mattysc42/IoT_midterm_remote/midterm_remote/src/playlist.h

#ifndef _PLAYLIST_H_
#define _PLAYLIST_H_

switch (currentTrack) {
    case 1: 
        myOLED.printf("Disturbed: \nRemnants");
        break;
    case 2: 
        myOLED.printf("Fastball: \nThe Way");
        break;
    case 3: 
        myOLED.printf("Periphery: \nPriestess");
        break;
    case 4: 
        myOLED.printf("Kansas: \nDust In The Wind");
        break;
    case 5: 
        myOLED.printf("Greenday: \nWake Me Up When \nSeptember Ends");
        break;
    case 6: 
        myOLED.printf("War of Ages: \nInstrumental");
        break;
    case 7: 
        myOLED.printf("Slipknot: \nSnuff");
        break;
    case 8: 
        myOLED.printf("Disturbed: \nThe Sound of\nSilence");
        break;
    case 9: 
        myOLED.printf("Demon Hunter: \nThe Tides Begin\nTo Rise");
        break;
    case 10: 
        myOLED.printf("10 Years\nThe Autumn\nEffect");
        break;
    case 11: 
        myOLED.printf("Breaking Benjamin:\nBlow Me Away");
        break;
    case 12: 
        myOLED.printf("Trivium:\nThe Sin And The\nSentence");
        break;
    case 13: 
        myOLED.printf("Avenged Sevenfold:\nUnholy Confessions");
        break;
    case 14: 
        myOLED.printf("Avenged Sevenfold:\nAfterlife");
        break;
    case 15: 
        myOLED.printf("Trivium:\nInto The Mouth Of\nHell We March");
        break;
    case 16: 
        myOLED.printf("Dragonforce:\nSoldiers Of The\nWasteland");
        break;
    case 17: 
        myOLED.printf("Periphery:\nFlatline");
        break;
    case 18: 
        myOLED.printf("Avenged Sevenfold:\nStrength Of The\nWorld");
        break;
    case 19: 
        myOLED.printf("Periphery:\nLune");
        break;
    case 20: 
        myOLED.printf("Trivium:\nThe Broken One");
        break;
    default:
        break;
};
#endif
